alagerkvist/E7020E-Project/Software/Rust/examples/codec.rs

#![no_main]
#![no_std]

extern crate cortex_m;
extern crate panic_halt;
//extern crate stm32f4;
extern crate stm32f4xx_hal as hal;
use crate::hal::prelude::*;
use cortex_m::{asm, iprintln};
use crate::hal::prelude::_stm32f4xx_hal_rcc_RccExt;
use hal::spi::{Spi, Mode, Phase, Polarity};
use hal::stm32::i2s2ext;
    use crate::hal::gpio::GpioExt as _stm32f4xx_hal_gpio_GpioExt;

use rtfm::{app};
#[app(device = hal::stm32)]
const APP: () = {

    #[init]
    fn init() {
        let stim = &mut core.ITM.stim[0];
        iprintln!(stim, "hello codec");
        
        device.RCC.cr.modify(|_,w| {
            w.plli2son().on()
            .hseon().on()
        });

        device.RCC.plli2scfgr.modify(|_,w| {
            unsafe {
                w.plli2sr().bits(0b100)
                .plli2sm().bits(0b110)
                .plli2sn().bits(0b10000010)
            }
        });
        // let mut rcc_cfgr = device.RCC.cfgr.read().bits();
        // rcc_cfgr &= 0xFF7FFFFF;
        device.RCC.cfgr.modify(|_, w| {
            w.i2ssrc().plli2s()
            // unsafe {
            //     w.bits(rcc_cfgr)
            // }
        });
        device.RCC.apb1enr.modify(|_, w| {
            w.spi2en().enabled()
        });

        device.RCC.ahb1enr.modify(|_, w| {
            w.gpioben().enabled()
            .gpiocen().enabled()
        });
        
        device.RCC.cfgr.modify(|_, w|  { 
            w.mco2().sysclk().mco2pre().div4() 
        });


        let rcc = device.RCC.constrain();
        let clocks = rcc.cfgr.freeze();
        
        let gpioa = device.GPIOA.split();
        let sck = gpioa.pa5.into_alternate_af5();
        let miso = gpioa.pa6.into_alternate_af5();
        let mosi = gpioa.pa7.into_alternate_af5();
        let mut cs = gpioa.pa4.into_push_pull_output();

        pub const MODE: Mode = Mode {
            polarity: Polarity::IdleHigh,
            phase: Phase::CaptureOnSecondTransition,
        };
        let mut spi = Spi::spi1(
            device.SPI1,
            (sck, miso, mosi),
            MODE,
            1_000_000.hz(),
            clocks
        );
        device.GPIOC.ospeedr.modify(|_, w| w.ospeedr6().very_high_speed());

        device.GPIOC.moder.modify(|_, w| w.moder9().alternate()); //bits(0b10));
        device.GPIOC.ospeedr.modify(|_, w| w.ospeedr9().very_high_speed()); // .bits(0b11));

        let gpioc = device.GPIOC.split();
        let _mclk = gpioc.pc6.into_alternate_af5();
        let gpiob = device.GPIOB.split();
        let _lrck = gpiob.pb12.into_alternate_af5();
        let _slck = gpiob.pb13.into_alternate_af5();
        let _sdin = gpiob.pb14.into_alternate_af6();
        let _sdout = gpiob.pb15.into_alternate_af5();

        device.I2S2EXT.i2spr.modify(|_, w| {
            unsafe{
                w.i2sdiv().bits(0b10)
            }
        });

        device.I2S2EXT.i2scfgr.modify(|_, w| {
            w.i2se().disabled()
        });

        device.I2S2EXT.i2scfgr.modify(|_, w| {
            w.i2smod().i2smode()
            .i2scfg().master_tx()
            .i2sstd().msb()
            .datlen().twenty_four_bit()
            .chlen().thirty_two_bit()
            .ckpol().idle_high()
        });

        device.I2S2EXT.i2scfgr.modify(|_, w| {
            w.i2se().enabled()
        });
        
        device.SPI2.i2scfgr.modify(|_, w| {
            w.i2se().disabled()
        });

        device.SPI2.i2scfgr.modify(|_, w| {
            w.i2smod().i2smode()
            .i2scfg().master_rx()
            .i2sstd().msb()
            .datlen().twenty_four_bit()
            .chlen().thirty_two_bit()
            .ckpol().idle_high()
        });

        device.SPI2.i2spr.modify(|_, w|{
            unsafe{
                w.mckoe().enabled()
                .i2sdiv().bits(0b10)
            }
        });
        device.SPI2.i2scfgr.modify(|_, w| {
            w.i2se().enabled()
        });
        
        
        cs.set_high();
        cs.set_low();
        cs.set_high();


        cs.set_low();
        let mut something = [0x9E, 0x04, 0x09];
        let  data = spi.transfer(&mut something);
        match data {
                Ok(v) => iprintln!(stim, "working with version: {:?}", v),
                Err(e) => iprintln!(stim, "error parsing header: {:?}", e),
        }
        cs.set_high();

        cs.set_low();
        let mut something = [0x9E, 0x06, 0x00];
        let  data = spi.transfer(&mut something);
        match data {
                Ok(v) => iprintln!(stim, "working with version: {:?}", v),
                Err(e) => iprintln!(stim, "error parsing header: {:?}", e),
        }
        cs.set_high();

        cs.set_low();
        let mut something = [0x9F, 0x04];
        let  data = spi.transfer(&mut something);
        match data {
                Ok(v) => iprintln!(stim, "working with version: {:?}", v),
                Err(e) => iprintln!(stim, "error parsing header: {:?}", e),
        }
        cs.set_high();
        
        

        /*
        asm::bkpt();
        loop {
            let mut buf: [u32; 1000] = [0;1000];
            let mut zeros = 0;
            
            for i in 0..1000 {
                while !device.SPI2.sr.read().rxne().bit_is_set(){}
                let byte = device.SPI2.dr.read().bits();
                buf[i] = byte;
                /*
                let sr = device.SPI2.sr.read();
                if sr.ovr().bit_is_set() {
                    //iprintln!(stim, "Ovr error!");
                } else if sr.udr().bit_is_set() {
                    //iprintln!(stim, "udr error!");
                } else if sr.fre().bit_is_set() {
                    //iprintln!(stim, "fre error!");
                } else if sr.rxne().bit_is_set() {
                    let byte = device.SPI2.dr.read().bits();
                    buf[i] = byte;
                } else {
                    //iprintln!(stim, "Would block!");
                }
                */
            }
            iprintln!(stim, "---------new data-------");
            for i in 0..1000 {
                if buf[i] == 0{
                    zeros += 1;
                }
                iprintln!(stim, "{:?}", buf[i]);
                for _ in 0..100{
                    asm::nop();
                }  
            }
            iprintln!(stim, "COUNT ZEROS: {:?}", zeros);
            asm::bkpt();
                // for _ in 0..10_000{
                //     asm::nop();
                // }
        }
        */
        // let mut something = [0x9E, 0x02, 0x40];
        // //let data = spi.write(&[0x9E, 0x84, 0x20]);
        // let  data = spi.transfer(&mut something);
        // match data {
        //         Ok(v) => iprintln!(stim, "working with version: {:?}", v),
        //         Err(e) => iprintln!(stim, "error parsing header: {:?}", e),
        // }
        // cs.set_high();

        // cs.set_low();
        // let mut something = [0x9E, 0x83, 0x41];
        // //let data = spi.write(&[0x9E, 0x84, 0x20]);
        // let  data = spi.transfer(&mut something);
        // match data {
        //         Ok(v) => iprintln!(stim, "working with version: {:?}", v),
        //         Err(e) => iprintln!(stim, "error parsing header: {:?}", e),
        // }
        // cs.set_high();
        /*
        cs.set_low();
        let mut something = [0x9E, 0x02, 0x60];
        let  data = spi.transfer(&mut something);
        match data {
                Ok(v) => iprintln!(stim, "working with version: {:?}", v),
                Err(e) => iprintln!(stim, "error parsing header: {:?}", e),
        }
        cs.set_high();

        cs.set_low();
        let mut something = [0x9E, 0x01];
        let  data = spi.transfer(&mut something);
        match data {
                Ok(v) => iprintln!(stim, "working with version: {:?}", v),
                Err(e) => iprintln!(stim, "error parsing header: {:?}", e),
        }
        cs.set_high();

        cs.set_low();
        let mut something = [0x9F, 0x01];
        let  data = spi.transfer(&mut something);
        //let data2 = spi.read();
        match data {
                Ok(v) => iprintln!(stim, "working with version: {:?}", v),
                Err(e) => iprintln!(stim, "error parsing header: {:?}", e),
        }
        //println!(stim, "{:?}", data2);
        cs.set_high();

        cs.set_low();
        let mut something = [0x9E, 0x02];
        let  data = spi.transfer(&mut something);
        match data {
                Ok(v) => iprintln!(stim, "working with version: {:?}", v),
                Err(e) => iprintln!(stim, "error parsing header: {:?}", e),
        }
        cs.set_high();

        cs.set_low();
        let mut something = [0x9F, 0x02];
        let  data = spi.transfer(&mut something);
        //let data2 = spi.read();
        match data {
                Ok(v) => iprintln!(stim, "working with version: {:?}", v),
                Err(e) => iprintln!(stim, "error parsing header: {:?}", e),
        }
        //println!(stim, "{:?}", data2);
        cs.set_high();
        */
        // asm::bkpt();
        // cs.set_low();
        // for _ in 1..10000 {
        //     asm::nop();
        // }
        // let mut something = [0x9F, 0x01];
        // //let mut something = [0x9F, 0x81, 0x82, 0x83, 0x84, 0x85, 0x86, 0x87, 0x08];
        
        // //let mut something = [0x9F, 0x02];
        // //let data = spi.write(&[0x9E, 0x84, 0x20]);
        // let  data = spi.transfer(&mut something);
        // let mut number: &[u8] = &[0x1];
        // match data {
        //         Ok(v) => {
        //             iprintln!(stim, "working with version: {:?}", v);
        //             number = v;
        //         },
        //         Err(e) => iprintln!(stim, "error parsing header: {:?}", e),
        // }
        // cs.set_high();
        
        // asm::bkpt();
        // //cs.set_low();
        // // iprintln!(stim, "{:?}", number);
        // // iprintln!(stim, "{:?}", number[1] & 0x5C);
        // cs.set_low();
        // for _ in 1..10000 {
        //     asm::nop();
        // }
        // spi.write(&[0x9E, 0x02, 0x41]);
        // // let mut something = [0x9E];
        // // //let mut something = [0x9F, 0x81, 0x82, 0x83, 0x84, 0x85, 0x86, 0x87, 0x08];
        
        // // //let mut something = [0x9F, 0x02];
        // // //let data = spi.write(&[0x9E, 0x84, 0x20]);
        // // let  data = spi.transfer(&mut something);
        // // match data {
        // //         Ok(v) => iprintln!(stim, "working with version: {:?}", v),
        // //         Err(e) => iprintln!(stim, "error parsing header: {:?}", e),
        // // }
        // // let mut something = [0x02];
        // // //let mut something = [0x9F, 0x81, 0x82, 0x83, 0x84, 0x85, 0x86, 0x87, 0x08];
        
        // // //let mut something = [0x9F, 0x02];
        // // //let data = spi.write(&[0x9E, 0x84, 0x20]);
        // // let  data = spi.transfer(&mut something);
        // // match data {
        // //         Ok(v) => iprintln!(stim, "working with version: {:?}", v),
        // //         Err(e) => iprintln!(stim, "error parsing header: {:?}", e),
        // // }
        // // let mut something = [0x40];
        // // //let mut something = [0x9F, 0x81, 0x82, 0x83, 0x84, 0x85, 0x86, 0x87, 0x08];
        
        // // //let mut something = [0x9F, 0x02];
        // // //let data = spi.write(&[0x9E, 0x84, 0x20]);
        // // let  data = spi.transfer(&mut something);
        // // match data {
        // //         Ok(v) => iprintln!(stim, "working with version: {:?}", v),
        // //         Err(e) => iprintln!(stim, "error parsing header: {:?}", e),
        // // }
        // cs.set_high();

        // asm::bkpt();
        // cs.set_low();
        // for _ in 1..10000 {
        //     asm::nop();
        // }
        // //let mut something = [0x9F, 0x05];
        // let mut something = [0x9F, 0x81, 0x82, 0x83, 0x84, 0x85, 0x86, 0x87, 0x08];
        
        // //let mut something = [0x9F, 0x02];
        // //let data = spi.write(&[0x9E, 0x84, 0x20]);
        // let  data = spi.transfer(&mut something);
        // //let mut number: &[u8] = &[0x1];
        // match data {
        //         Ok(v) => {
        //             iprintln!(stim, "working with version: {:?}", v);
        //             //number = v;
        //         },
        //         Err(e) => iprintln!(stim, "error parsing header: {:?}", e),
        // }
        // cs.set_high();
                //     let sr = device.SPI3.sr.read();
        /*
        let mut done = false;
        while !done {
            let sr = device.SPI3.sr.read();
            if sr.rxne().bit_is_set() {
                done = true;
            }
        }
        let data = spi.read();
        */
        
        // let data = spi.write(&[0x04]);
        // match data {
        //         Ok(v) => iprintln!(stim, "working with version: {:?}", v),
        //         Err(e) => iprintln!(stim, "error parsing header: {:?}", e),
        // }
        // let data = spi.write(&[0x20]);
        // match data {
        //         Ok(v) => iprintln!(stim, "working with version: {:?}", v),
        //         Err(e) => iprintln!(stim, "error parsing header: {:?}", e),
        // }
        
        // cs.set_low();
        
        // let data = spi.write(&[0x9E, 0x06, 0x00]);
        // match data {
        //         Ok(v) => iprintln!(stim, "working with version: {:?}", v),
        //         Err(e) => iprintln!(stim, "error parsing header: {:?}", e),
        // }
        // cs.set_high();

        // cs.set_low();
        
        // let data = spi.write(&[0x9E, 0x08, 0x00]);
        // match data {
        //         Ok(v) => iprintln!(stim, "working with version: {:?}", v),
        //         Err(e) => iprintln!(stim, "error parsing header: {:?}", e),
        // }
        // cs.set_high();

        // cs.set_low();
        
        // let data = spi.write(&[0x9E, 0x08, 0x00]);
        // match data {
        //         Ok(v) => iprintln!(stim, "working with version: {:?}", v),
        //         Err(e) => iprintln!(stim, "error parsing header: {:?}", e),
        // }
        // cs.set_high();
        /*
        let gpiob = device.GPIOB.split();
        let lrck = gpiob.pb12.into_alternate_af5();
        let slck = gpiob.pb13.into_alternate_af5();
        let sdin = gpiob.pb14.into_alternate_af6();
        let sdout = gpiob.pb15.into_alternate_af5();

        let mut button4 = gpiob.pb4.into_pull_up_input();
        let mut button5 = gpiob.pb5.into_pull_up_input();
        */

       
        // A full cycle, 16-bit, 2's complement Sine wave lookup table
        // let sine: [i32; 256] = [
        // 0x0000, 0x0324, 0x0647, 0x096a, 0x0c8b, 0x0fab, 0x12c8, 0x15e2, 
        // 0x18f8, 0x1c0b, 0x1f19, 0x2223, 0x2528, 0x2826, 0x2b1f, 0x2e11,
        // 0x30fb, 0x33de, 0x36ba, 0x398c, 0x3c56, 0x3f17, 0x41ce, 0x447a, 
        // 0x471c, 0x49b4, 0x4c3f, 0x4ebf, 0x5133, 0x539b, 0x55f5, 0x5842,
        // 0x5a82, 0x5cb4, 0x5ed7, 0x60ec, 0x62f2, 0x64e8, 0x66cf, 0x68a6, 
        // 0x6a6d, 0x6c24, 0x6dca, 0x6f5f, 0x70e2, 0x7255, 0x73b5, 0x7504,
        // 0x7641, 0x776c, 0x7884, 0x798a, 0x7a7d, 0x7b5d, 0x7c29, 0x7ce3, 
        // 0x7d8a, 0x7e1d, 0x7e9d, 0x7f09, 0x7f62, 0x7fa7, 0x7fd8, 0x7ff6,
        // 0x7fff, 0x7ff6, 0x7fd8, 0x7fa7, 0x7f62, 0x7f09, 0x7e9d, 0x7e1d, 
        // 0x7d8a, 0x7ce3, 0x7c29, 0x7b5d, 0x7a7d, 0x798a, 0x7884, 0x776c,
        // 0x7641, 0x7504, 0x73b5, 0x7255, 0x70e2, 0x6f5f, 0x6dca, 0x6c24, 
        // 0x6a6d, 0x68a6, 0x66cf, 0x64e8, 0x62f2, 0x60ec, 0x5ed7, 0x5cb4,
        // 0x5a82, 0x5842, 0x55f5, 0x539b, 0x5133, 0x4ebf, 0x4c3f, 0x49b4, 
        // 0x471c, 0x447a, 0x41ce, 0x3f17, 0x3c56, 0x398c, 0x36ba, 0x33de,
        // 0x30fb, 0x2e11, 0x2b1f, 0x2826, 0x2528, 0x2223, 0x1f19, 0x1c0b, 
        // 0x18f8, 0x15e2, 0x12c8, 0x0fab, 0x0c8b, 0x096a, 0x0647, 0x0324,
        // 0x0000, 0xfcdc, 0xf9b9, 0xf696, 0xf375, 0xf055, 0xed38, 0xea1e, 
        // 0xe708, 0xe3f5, 0xe0e7, 0xdddd, 0xdad8, 0xd7da, 0xd4e1, 0xd1ef,
        // 0xcf05, 0xcc22, 0xc946, 0xc674, 0xc3aa, 0xc0e9, 0xbe32, 0xbb86, 
        // 0xb8e4, 0xb64c, 0xb3c1, 0xb141, 0xaecd, 0xac65, 0xaa0b, 0xa7be,
        // 0xa57e, 0xa34c, 0xa129, 0x9f14, 0x9d0e, 0x9b18, 0x9931, 0x975a, 
        // 0x9593, 0x93dc, 0x9236, 0x90a1, 0x8f1e, 0x8dab, 0x8c4b, 0x8afc,
        // 0x89bf, 0x8894, 0x877c, 0x8676, 0x8583, 0x84a3, 0x83d7, 0x831d, 
        // 0x8276, 0x81e3, 0x8163, 0x80f7, 0x809e, 0x8059, 0x8028, 0x800a,
        // 0x8000, 0x800a, 0x8028, 0x8059, 0x809e, 0x80f7, 0x8163, 0x81e3, 
        // 0x8276, 0x831d, 0x83d7, 0x84a3, 0x8583, 0x8676, 0x877c, 0x8894,
        // 0x89bf, 0x8afc, 0x8c4b, 0x8dab, 0x8f1e, 0x90a1, 0x9236, 0x93dc, 
        // 0x9593, 0x975a, 0x9931, 0x9b18, 0x9d0e, 0x9f14, 0xa129, 0xa34c,
        // 0xa57e, 0xa7be, 0xaa0b, 0xac65, 0xaecd, 0xb141, 0xb3c1, 0xb64c, 
        // 0xb8e4, 0xbb86, 0xbe32, 0xc0e9, 0xc3aa, 0xc674, 0xc946, 0xcc22,
        // 0xcf05, 0xd1ef, 0xd4e1, 0xd7da, 0xdad8, 0xdddd, 0xe0e7, 0xe3f5, 
        // 0xe708, 0xea1e, 0xed38, 0xf055, 0xf375, 0xf696, 0xf9b9, 0xfcdc,
        // ];
        // 
        // const PI: f32 = 3.14159265358979323846;
        // const TAU: f32 = (2.0 * PI);
        // let sine: [i32; nSamples];
        // let mut i = 0;
        // while(i < nSamples) {
        //     let t: f32 = ((i as f32)/2.0)/(nSamples as f32);
        //     sine[i] = 3.14.sine();//8388601*sin(100.0 * t * TAU); // left
        //     sine[i+1] = sine[i]; // right
        //     i += 2;
        // }


        
        const nSamples: usize = 1000;
        //let sine: [i32; nSamples] = [0xAAABAB];
        let sine: [i32; nSamples] = [0x0,0x4b4d37,0x79c8ee,0x79a90e,0x4af9cb,0xff98f5,0xb45f8d,0x861781,0x867720,0xb559d3,0xce17,0x4bf37d,0x7a07c1,0x796863,0x4a5260,0xfecade,0xb3b9a9,0x85d94c,0x86b86a,0xb6019e,0x19c2d,0x4c98ff,0x7a4557,0x79267c,0x49aa35,0xfdfcca,0xb3148b,0x859c55,0x86faed,0xb6aa28,0x26a3e,0x4d3db9,0x7a81b0,0x78e35b,0x49014b,0xfd2ebc,0xb27034,0x85609a,0x873eab,0xb75371,0x33849,0x4de1ac,0x7abccc,0x789f01,0x4857a3,0xfc60b4,0xb1cca6,0x85261d,0x8783a1,0xb7fd77,0x4064c,0x4e84d5,0x7af6aa,0x78596e,0x47ad40,0xfb92b7,0xb129e3,0x84ecdf,0x87c9d0,0xb8a837,0x4d444,0x4f2732,0x7b2f48,0x7812a3,0x470224,0xfac4c4,0xb087ec,0x84b4e0,0x881137,0xb953b0,0x5a230,0x4fc8c2,0x7b66a8,0x77caa1,0x46564f,0xf9f6e0,0xafe6c4,0x847e21,0x8859d5,0xb9ffe0,0x6700d,0x506983,0x7b9cc7,0x778168,0x45a9c4,0xf9290b,0xaf466b,0x8448a1,0x88a3a8,0xbaacc6,0x73dd9,0x510973,0x7bd1a6,0x7736fa,0x44fc84,0xf85b47,0xaea6e3,0x841463,0x88eeb1,0xbb5a5f,0x80b93,0x51a892,0x7c0544,0x76eb56,0x444e91,0xf78d98,0xae082e,0x83e165,0x893aef,0xbc08aa,0x8d938,0x5246dd,0x7c37a1,0x769e7e,0x439fee,0xf6bffe,0xad6a4e,0x83afaa,0x898861,0xbcb7a6,0x9a6c6,0x52e452,0x7c68bb,0x765073,0x42f09b,0xf5f27c,0xaccd43,0x837f30,0x89d706,0xbd6750,0xa743b,0x5380f1,0x7c9893,0x760135,0x42409a,0xf52515,0xac3111,0x834ffa,0x8a26dd,0xbe17a7,0xb4195,0x541cb7,0x7cc728,0x75b0c5,0x418fee,0xf457c9,0xab95b7,0x832207,0x8a77e6,0xbec8a8,0xc0ed1,0x54b7a3,0x7cf47a,0x755f24,0x40de98,0xf38a9c,0xaafb39,0x82f557,0x8aca1f,0xbf7a53,0xcdbee,0x5551b4,0x7d2087,0x750c52,0x402c99,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
        asm::bkpt();
        loop {
            for _ in 0..10 {
                for i in 0..8388608 {
                    let low = ((i & 0xFF) << 8) as u16;
                    let high = ((i & 0xFFFF00) >> 8) as u16;
                    while !device.SPI2.sr.read().txe().bit_is_set() {}
                    device.I2S2EXT.dr.write(|w| unsafe { w.dr().bits(high)});
                    while !device.SPI2.sr.read().txe().bit_is_set() {}
                    device.I2S2EXT.dr.write(|w| unsafe { w.dr().bits(low)});
                    
                }
                asm::bkpt();
            }
        }

        loop {
            for _ in 0..10 {
                for i in 0..nSamples {
                    //let low = ((sine[i] & 0xFF) << 8) as u16;
                    //let high = ((sine[i] & 0xFFFF00) >> 8) as u16;
                    /*
                    while !device.SPI2.sr.read().txe().bit_is_set() {}
                    //device.SPI2.dr.write(|w| unsafe { w.dr().bits(0xAAAA)});
                    device.SPI2.dr.write(|w| unsafe { w.dr().bits(high)});
                    while !device.SPI2.sr.read().txe().bit_is_set() {}
                    //device.SPI2.dr.write(|w| unsafe { w.dr().bits(0xBA00)});
                    
                    device.SPI2.dr.write(|w| unsafe { w.dr().bits(low)});
                    */
                    while !device.I2S2EXT.sr.read().txe().bit_is_set() {}
                    //device.I2S2EXT.dr.write(|w| unsafe { w.dr().bits(high)});
                    device.I2S2EXT.dr.write(|w| unsafe { w.dr().bits(0x7FFF)});
                    while !device.I2S2EXT.sr.read().txe().bit_is_set() {}
                    device.I2S2EXT.dr.write(|w| unsafe { w.dr().bits(0x01)});
                    //device.I2S2EXT.dr.write(|w| unsafe { w.dr().bits(low)});
                }
            }
            asm::bkpt();
        }
    }
    
    #[idle]
    fn idle() -> ! {
        loop {
            asm::wfi();
        }
    }

    //#[interrupt]

};
